borpendy/Dspi3/Print files/BodyParts/top cover.stl

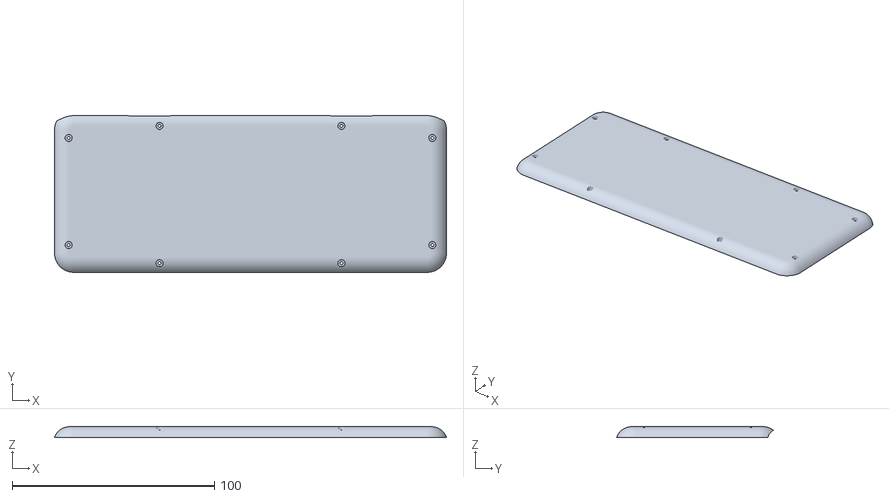
[picture p15: CAD file, 2026-08-11]
Print files/BodyParts/top cover.stl
194.0 x 77.6 x 5.30
