borpendy/Dspi3/Print files/Buttons/A.stl

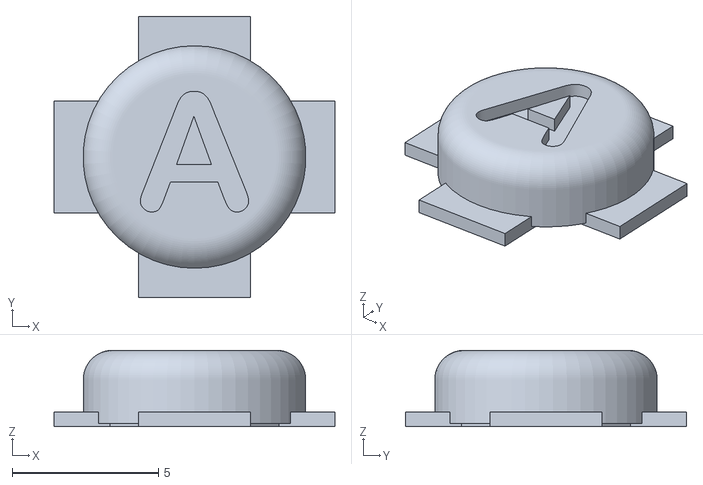
[picture p16: CAD file, 2026-08-11]
Print files/Buttons/A.stl
9.60 x 9.60 x 2.61
