borpendy/Dspi3/Print files/BodyParts/hinge_l_inner.stl

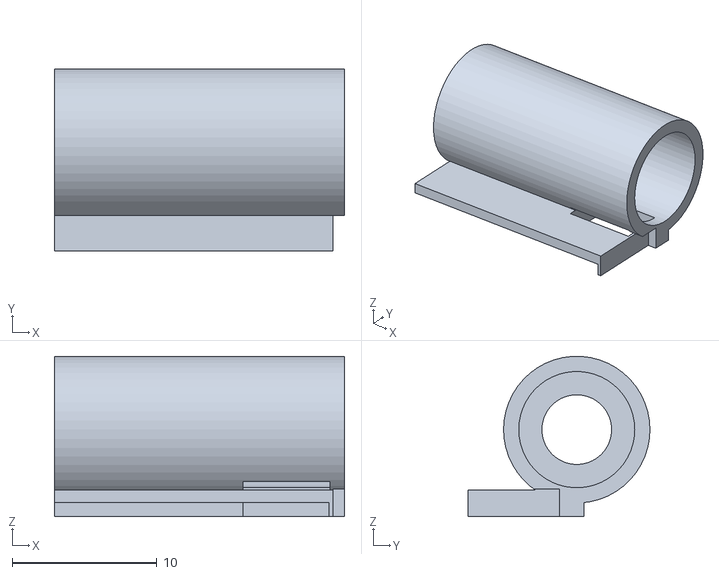
[picture p17: CAD file, 2026-08-11]
Print files/BodyParts/hinge_l_inner.stl
20.0 x 12.5 x 11.1
