borpendy/Dspi3/Print files/BodyParts/hinge_m.stl

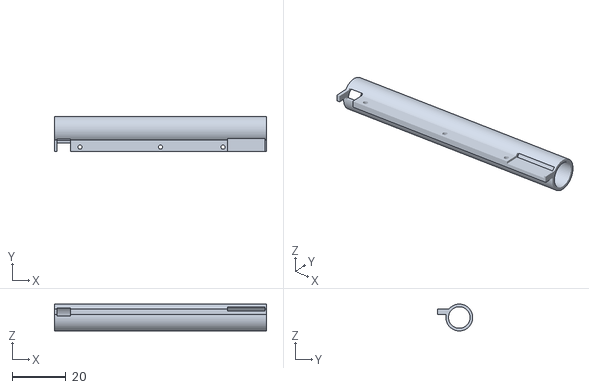
[picture p18: CAD file, 2026-06-14]
Print files/BodyParts/hinge_m.stl
79.0 x 13.2 x 10.0
