borpendy/Dspi3/Print files/Buttons/X.stl

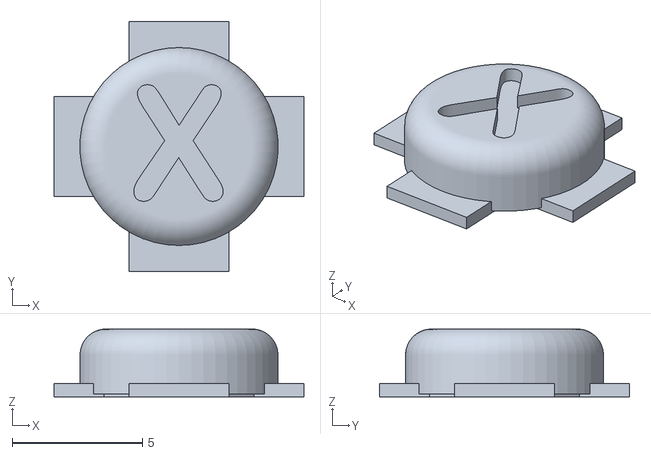
[picture p19: CAD file, 2026-08-11]
Print files/Buttons/X.stl
9.60 x 9.60 x 2.61
